UgoesSky/VERSION2/Hardware/GY80/GY88_3.3v_LAYOUT.png

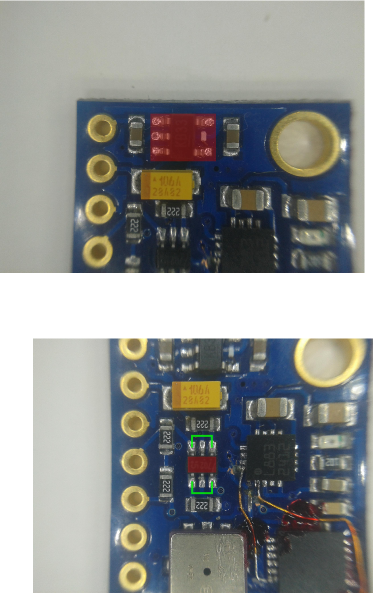
Hardware/GY80/GY88_3.3v_LAYOUT.png
