UgoesSky/VERSION2/Hardware/GY80/GY88_top2.jpg

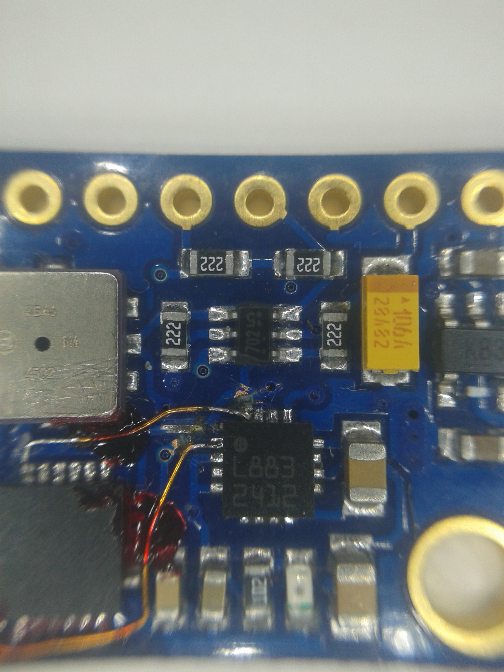
Hardware/GY80/GY88_top2.jpg
