UgoesSky/VERSION2/Hardware/GY80/GY_88.jpg

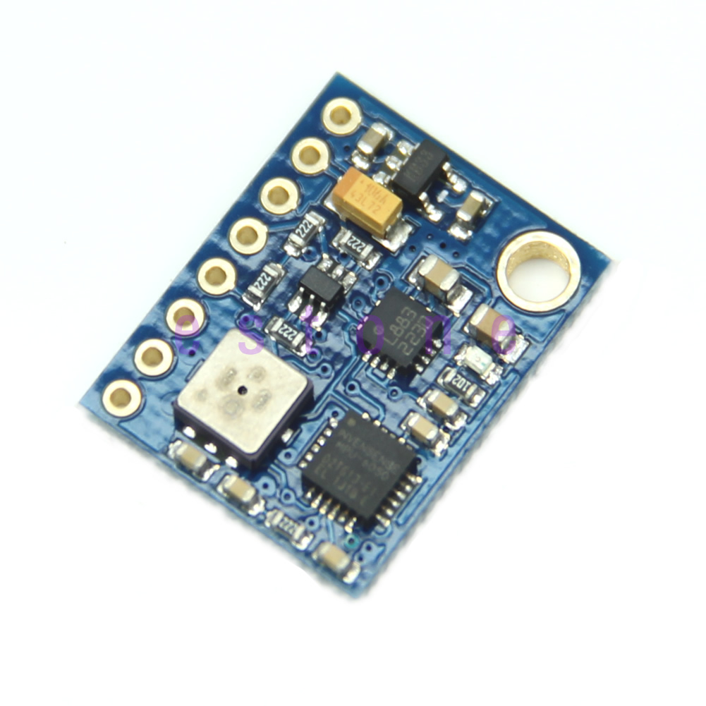
Hardware/GY80/GY_88.jpg
