UgoesSky/VERSION2/Hardware/Umweltdaten/Bilder/bottom.png

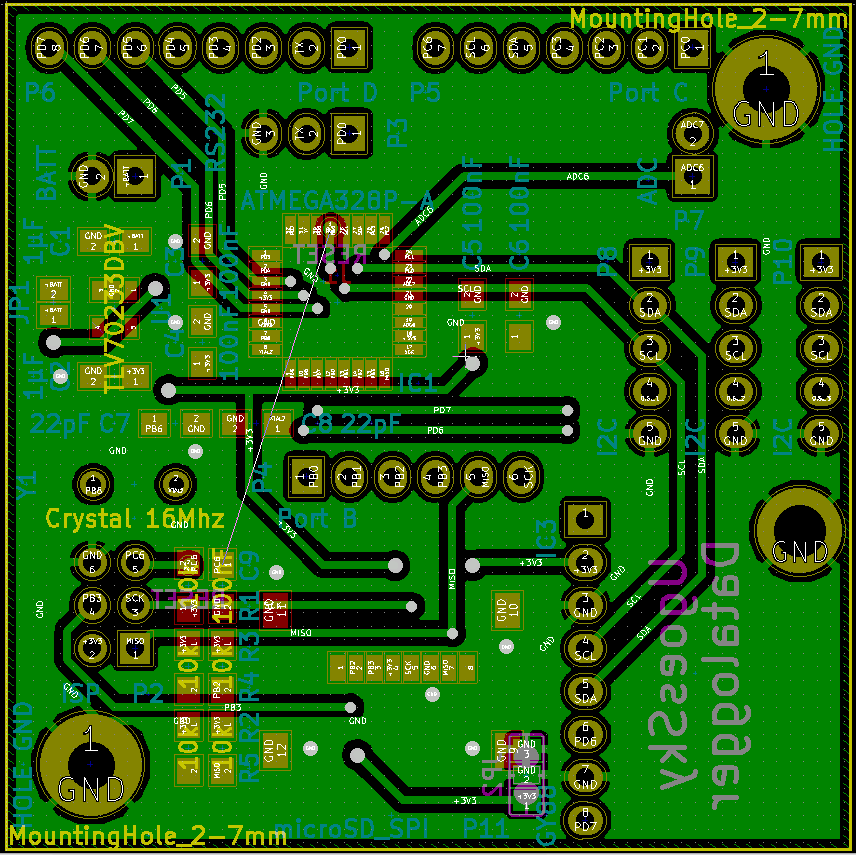
Hardware/Umweltdaten/Bilder/bottom.png
