UgoesSky/VERSION2/Hardware/Umweltdaten/Bilder/bottom_3d.png

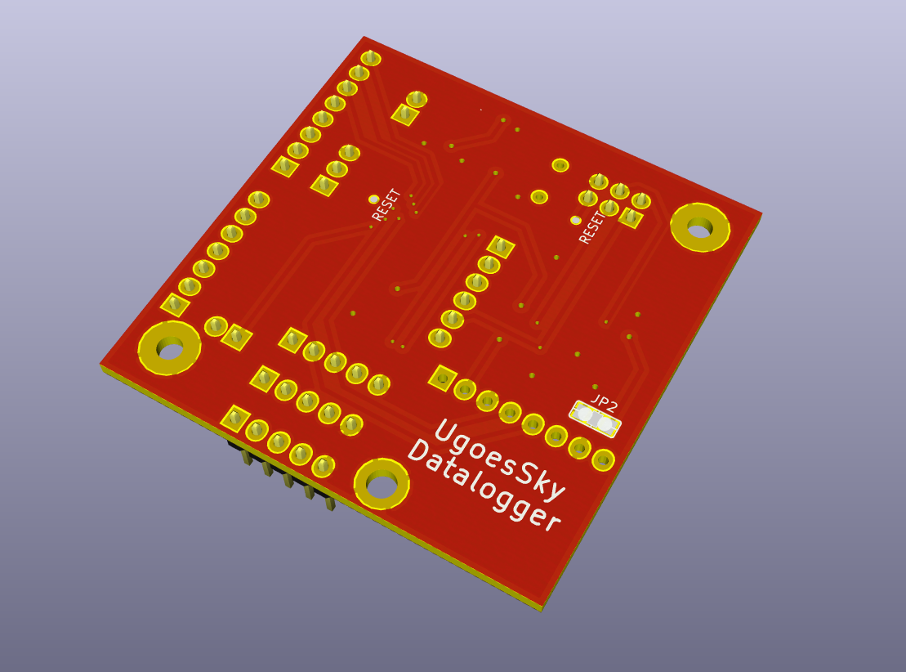
Hardware/Umweltdaten/Bilder/bottom_3d.png
