UgoesSky/VERSION2/Hardware/Umweltdaten/Bilder/top.png

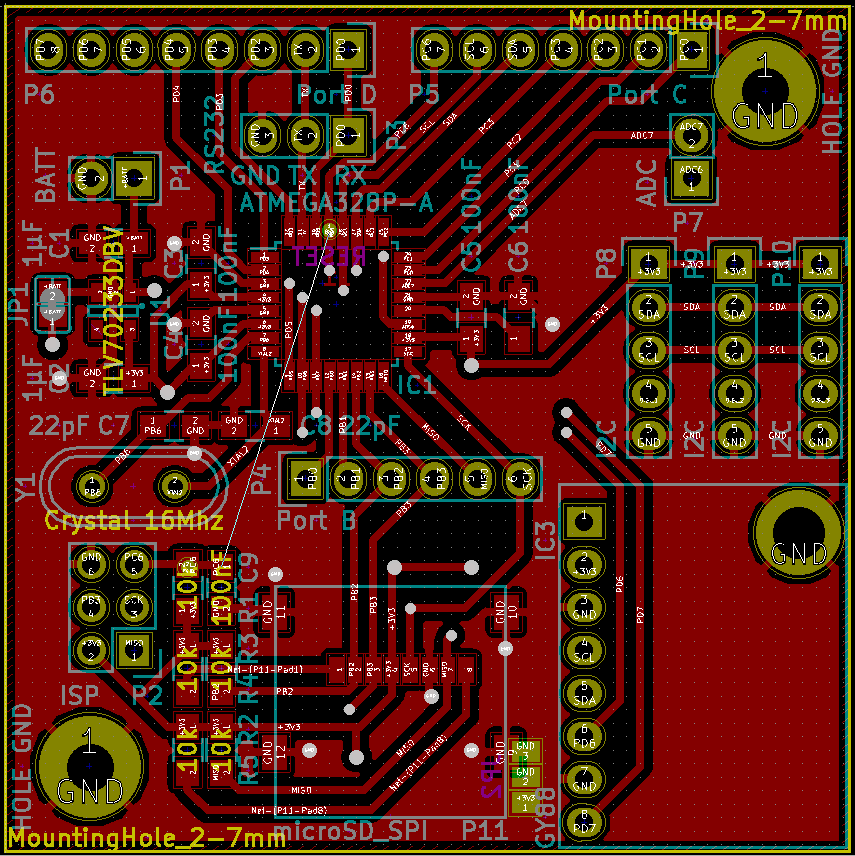
Hardware/Umweltdaten/Bilder/top.png
