UgoesSky/VERSION2/Hardware/Umweltdaten/LM75/3D.png

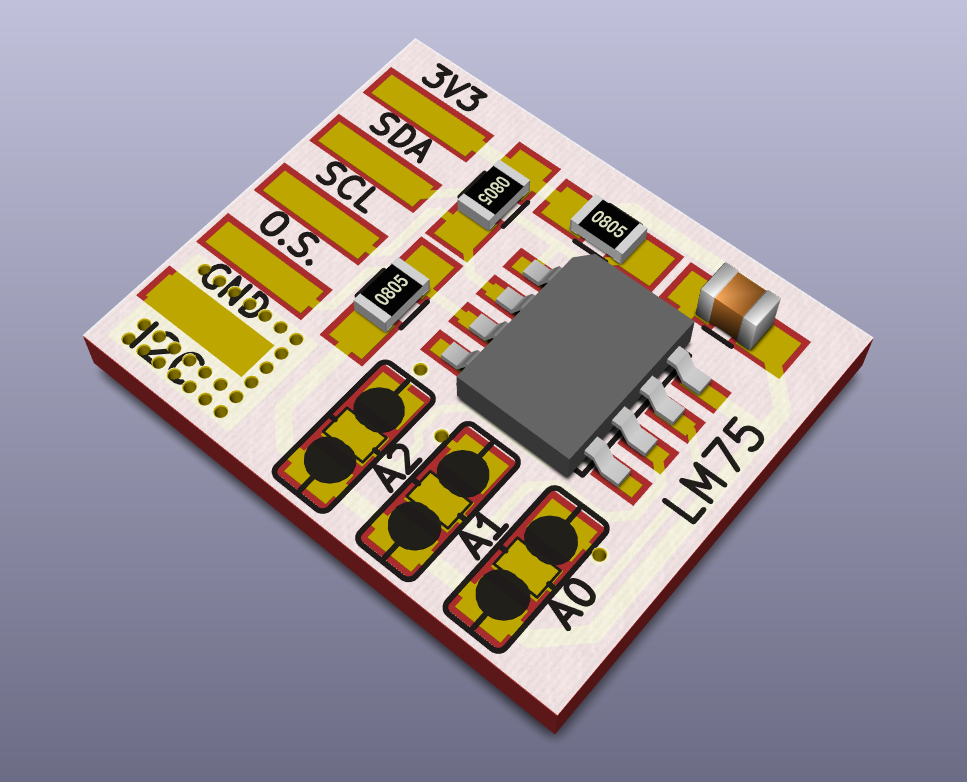
Hardware/Umweltdaten/LM75/3D.png
